friedpies/moon-germs/Assets/front_right_transparent.png

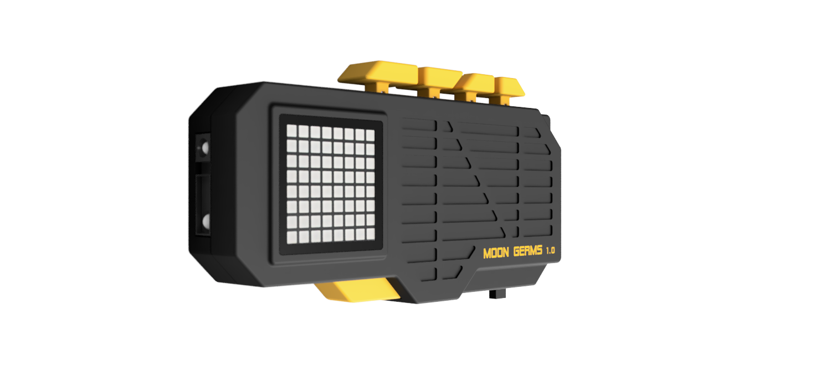
Assets/front_right_transparent.png
