friedpies/moon-germs/Assets/front_right_transparent_black.png

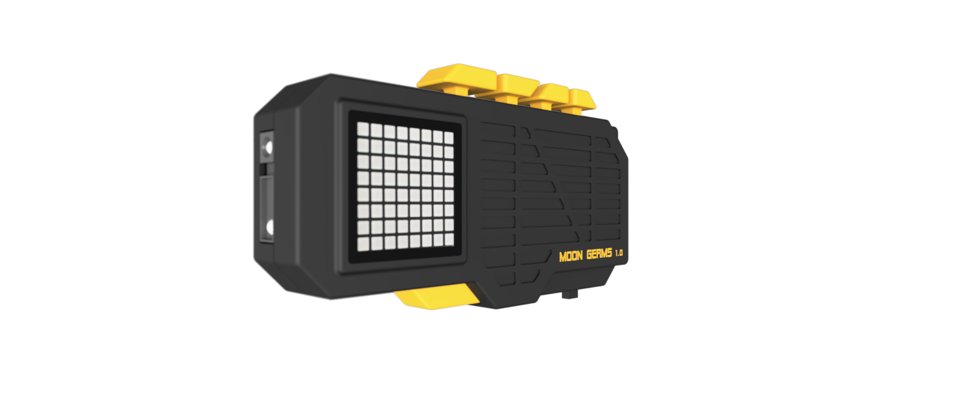
Assets/front_right_transparent_black.png
