friedpies/moon-germs/Assets/inside.jpg

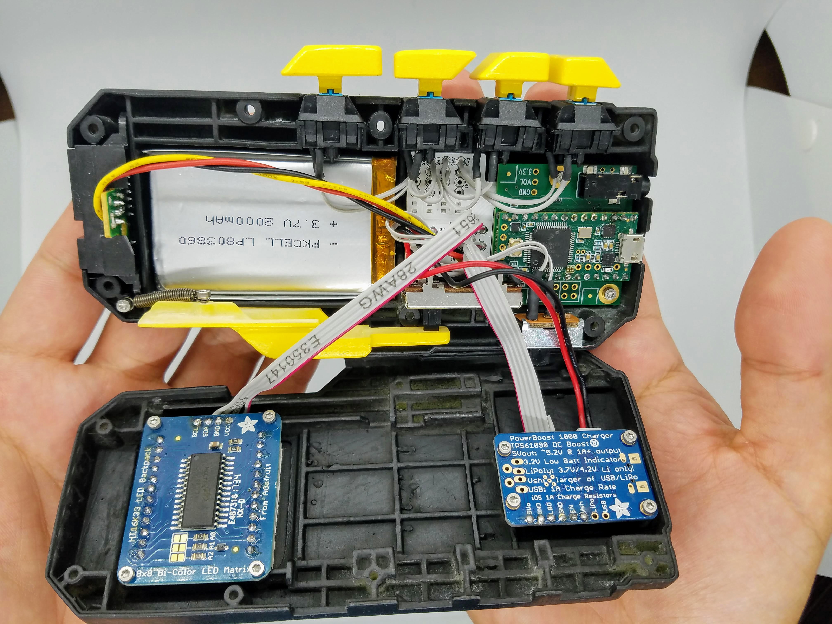
Assets/inside.jpg
