friedpies/moon-germs/Assets/MOON_GERMS_RENDER_BELOW.png

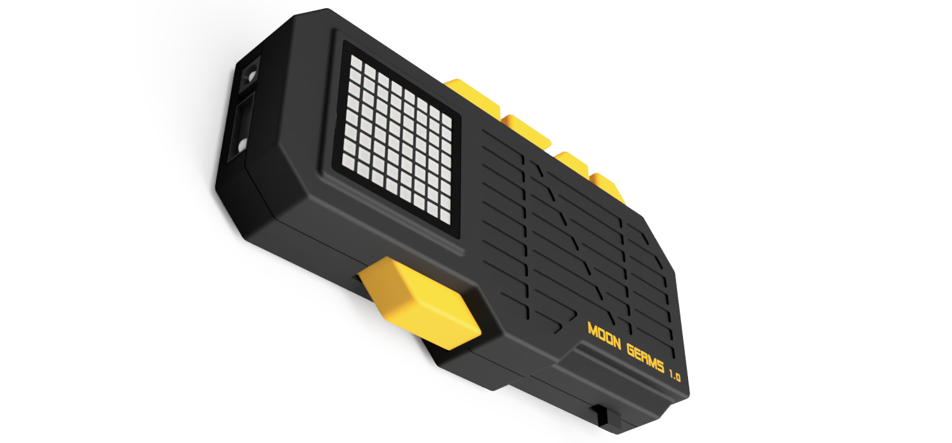
Assets/MOON_GERMS_RENDER_BELOW.png
