friedpies/moon-germs/Assets/MOON_GERMS_RENDER_FRONT.png

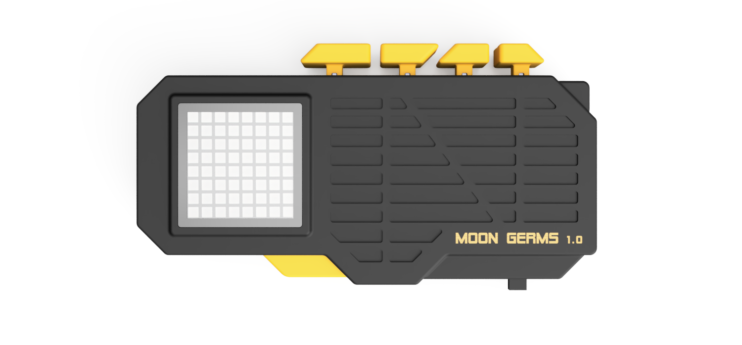
Assets/MOON_GERMS_RENDER_FRONT.png
