friedpies/moon-germs/Assets/synthengine.png

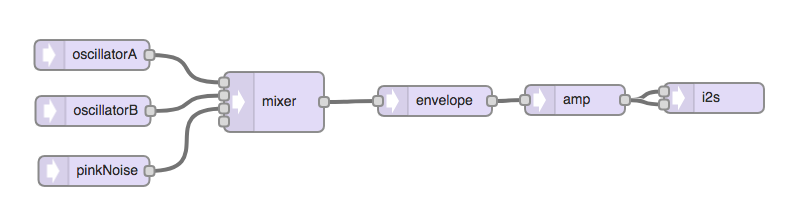
Assets/synthengine.png
