friedpies/moon-germs/Assets/teensy_pins.jpg

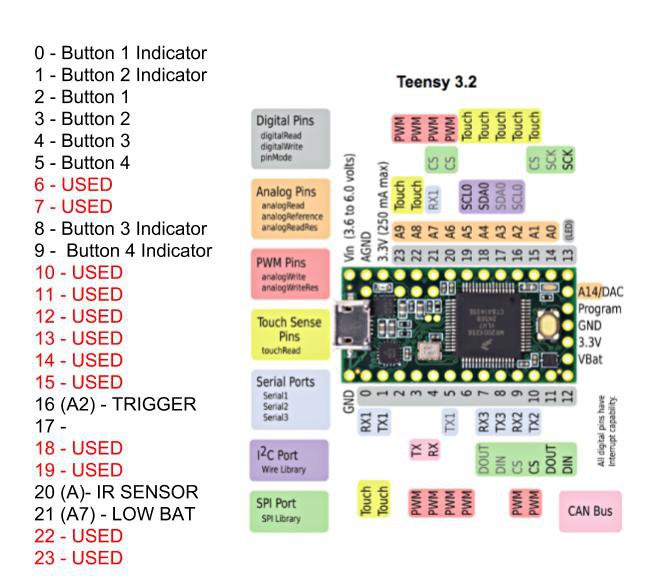
Assets/teensy_pins.jpg
