friedpies/moon-germs/Desktop App/moon_germs_app/application.macosx/moon_germs_app.app/Contents/Java/data/drawing-overlay.png

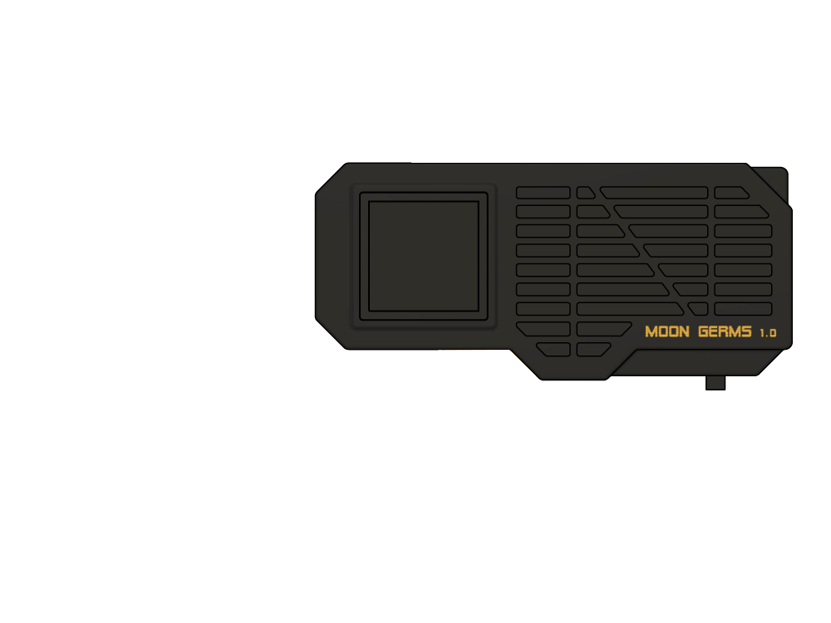
Desktop App/moon_germs_app/application.macosx/moon_germs_app.app/Contents/Java/data/drawing-overlay.png
