friedpies/moon-germs/Photos/app_device_small.gif

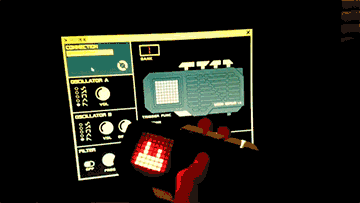
Photos/app_device_small.gif
