friedpies/moon-germs/Photos/cycles.gif

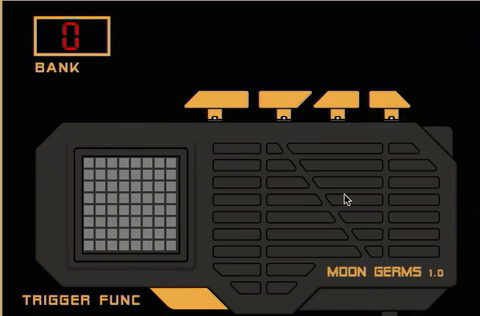
Photos/cycles.gif
