friedpies/moon-germs/Arduino/moonGerms/bitMaps.h

// Contains frames for various display animations

static uint8_t PROGMEM
emptyBMP[8] = {
  B00000000, // Frame 1
  B00000000,
  B00000000,
  B00000000,
  B00000000,
  B00000000,
  B00000000,
  B00000000
};

static uint8_t PROGMEM plugBMP[][8] = {
  {
    B00000000, // Frame 1
    B00000000,
    B00000000,
    B00000000,
    B00000000,
    B00000000,
    B00000000,
    B00000000
  }, {
    B00000000, // Frame 2
    B00000000,
    B00000000,
    B00000000,
    B00000000,
    B00000000,
    B00000000,
    B00100100
  }, {
    B00000000, // Frame 3
    B00000000,
    B00000000,
    B00000000,
    B00000000,
    B00000000,
    B00100100,
    B00100100
  }, {
    B00000000, // Frame 4
    B00000000,
    B00000000,
    B00000000,
    B00000000,
    B00100100,
    B00100100,
    B00100100
  }, {
    B00000000, // Frame 5
    B00000000,
    B00000000,
    B00000000,
    B00100100,
    B00100100,
    B00100100,
    B01111110
  }, {
    B00000000, // Frame 6
    B00000000,
    B00000000,
    B00100100,
    B00100100,
    B00100100,
    B01111110,
    B01111110
  }, {
    B00000000, // Frame 7
    B00000000,
    B00100100,
    B00100100,
    B00100100,
    B01111110,
    B01111110,
    B00111100
  }, {
    B00000000, // Frame 8
    B00100100,
    B00100100,
    B00100100,
    B01111110,
    B01111110,
    B00111100,
    B00011000
  }, {
    B00100100, // Frame 9
    B00100100,
    B00100100,
    B01111110,
    B01111110,
    B00111100,
    B00011000,
    B00011000
  }, {
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
    B01100000,
    B00000000
  },
  { B00000000, // Frame 14
    B00000000,
    B00000000,
    B00000000,
    B00000000,
    B00000000,
    B00000000,
    B00000000
  },
  { B00000000, // Frame 15
    B10000100,
    B01111110,
    B01101010,
    B01101010,
    B01101010,
    B01101011,
    B00000000
  },
  { B00000000, // Frame 16
    B00000000,
    B00000000,
    B00000000,
    B00000000,
    B00000000,
    B00000000,
    B00000000
  },
  { B00000000, // Frame 17
    B00111100,
    B01100110,
    B00110000,
    B00001100,
    B01100110,
    B00111100,
    B00000000
  },
  { B00000000, // Frame 18
    B00000000,
    B00000000,
    B00000000,
    B00000000,
    B00000000,
    B00000000,
    B00000000
  },
};
